MartinMelo/DomiticTIP/Documentacion/Esquema.png

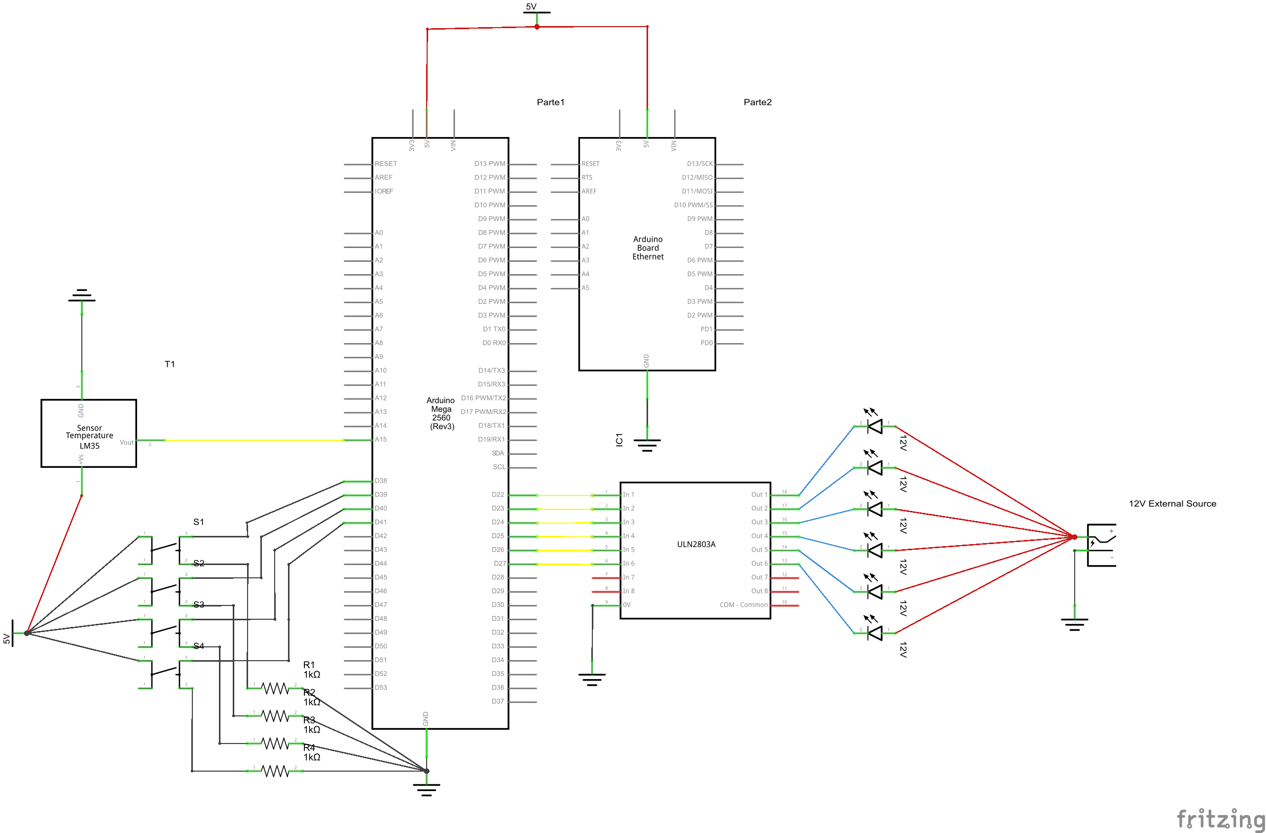
Documentacion/Esquema.png
