MartinMelo/DomiticTIP/public/modules/widgets/img/temperatura.png

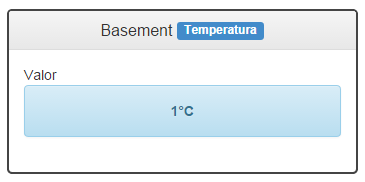
public/modules/widgets/img/temperatura.png
